kirakage88/thesis/schematics/kicad_templates-master/Alchitry_Au/meta/info.html

# Alchitry Shield Board

This template creates the basic layout for designing an Alchitry (https://alchitry.com/) shield

This base project includes the PCB edge with 4x 50-pin headers and mounting holes in the correct position. This also includes the footprint library and schmatic symbols for the bottom, male connectors. The connectors are numbered such that pin B1 aligns with pin X1 on the Alchitry board for easy reference to the Alchitry datasheet.

The board outline looks like the following:

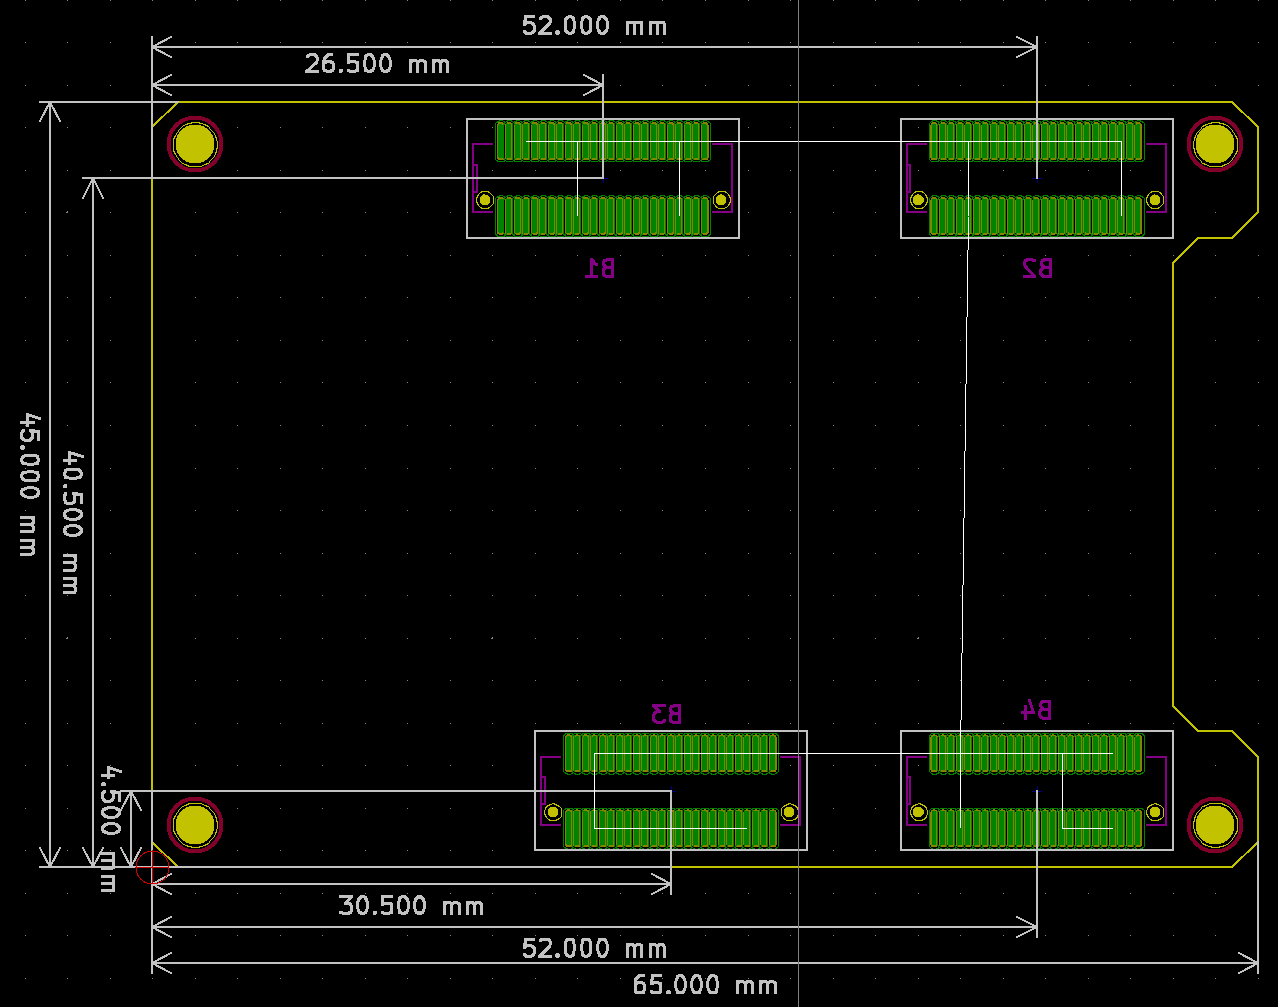
[picture p1: schematics/kicad_templates-master/Alchitry_Au/meta/board.png]
