kirakage88/thesis/designs/tft_display/assets/home_page.png

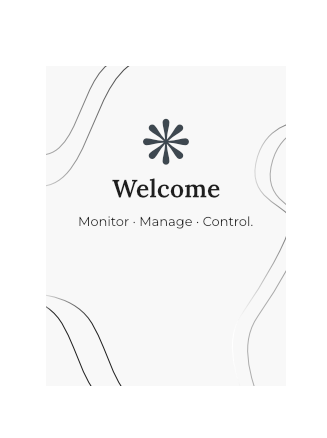
designs/tft_display/assets/home_page.png
