kirakage88/thesis/designs/tft_display/home_page.png

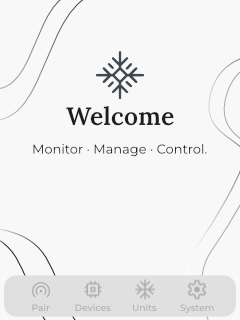
designs/tft_display/home_page.png
