kirakage88/thesis/designs/tft_display/init_page.png

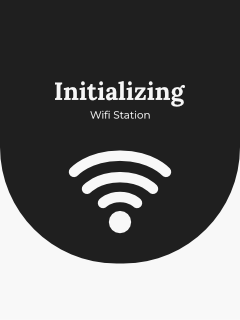
designs/tft_display/init_page.png
