kirakage88/thesis/designs/tft_display/palette_shades.png

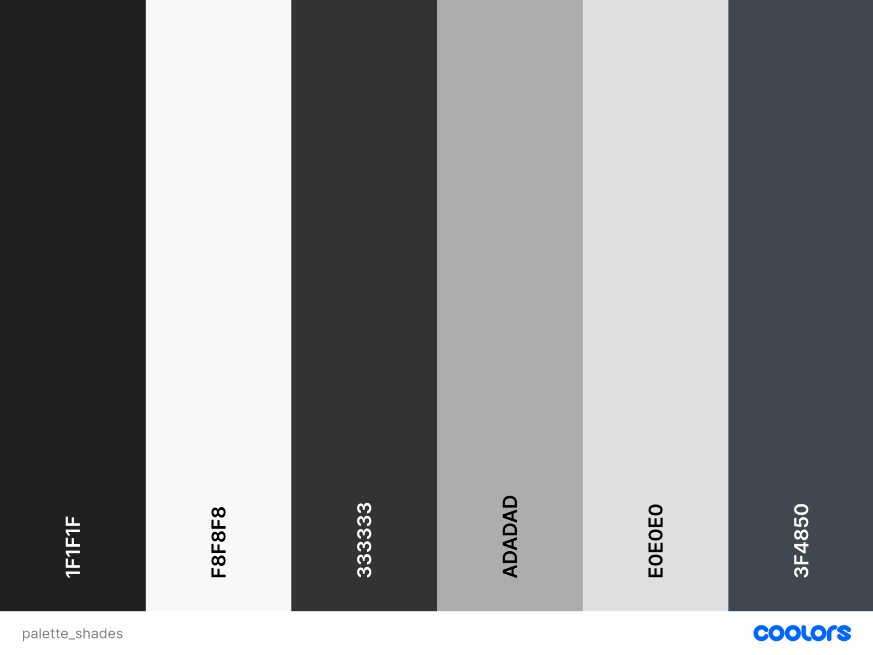
designs/tft_display/palette_shades.png
