kirakage88/thesis/designs/website/reference_website.jpg

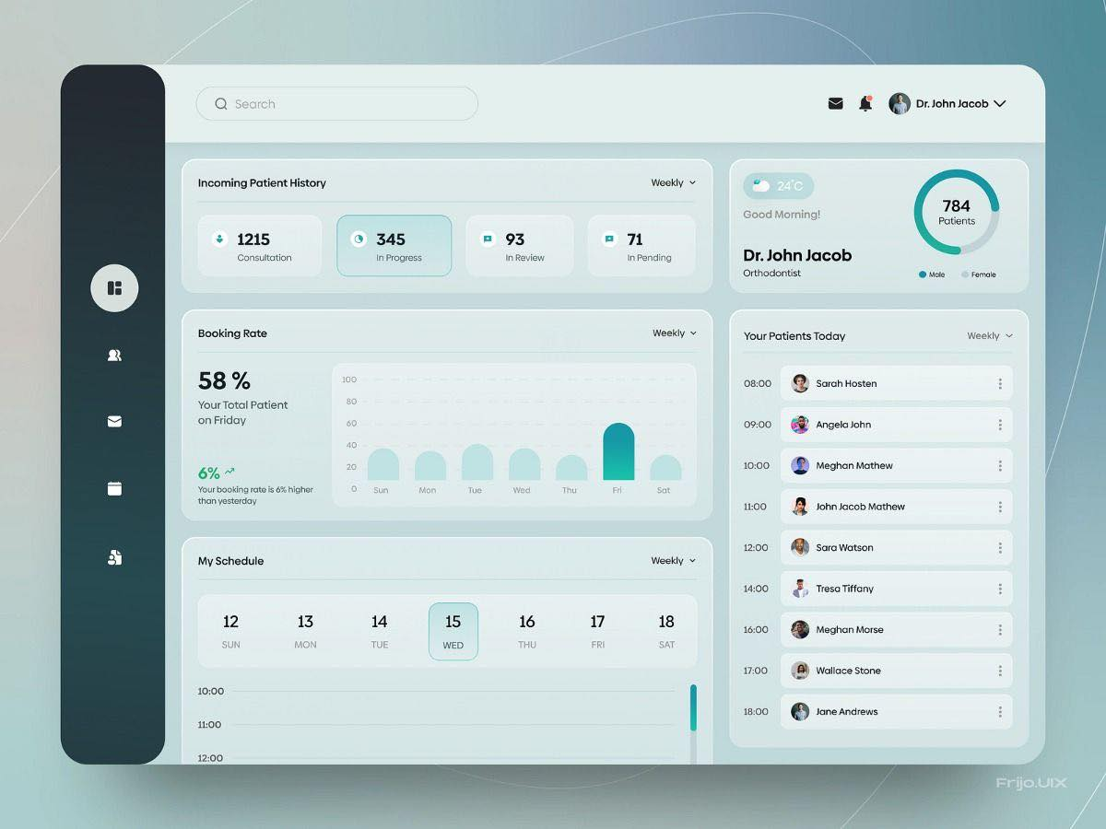
designs/website/reference_website.jpg
