kirakage88/thesis/schematics/BME 280 SOLO.jpg

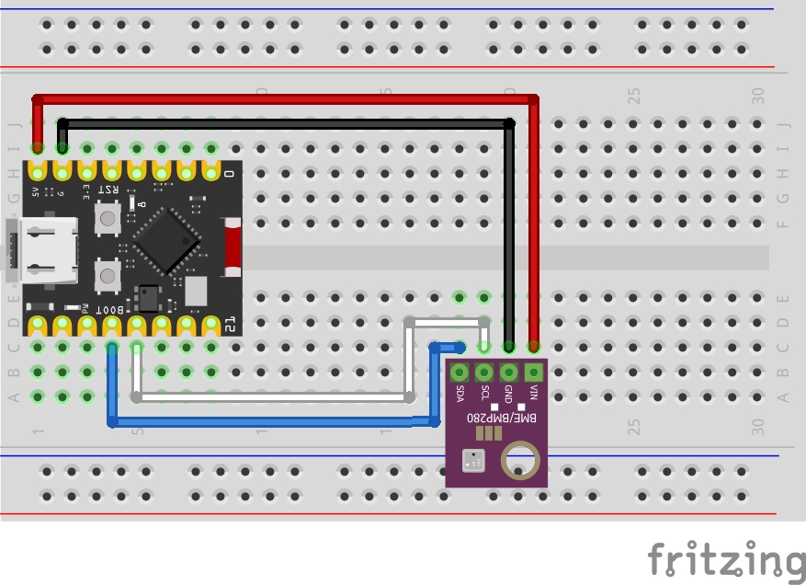
schematics/BME 280 SOLO.jpg
