kirakage88/thesis/schematics/RMS Prototype Ver 1_bb.png

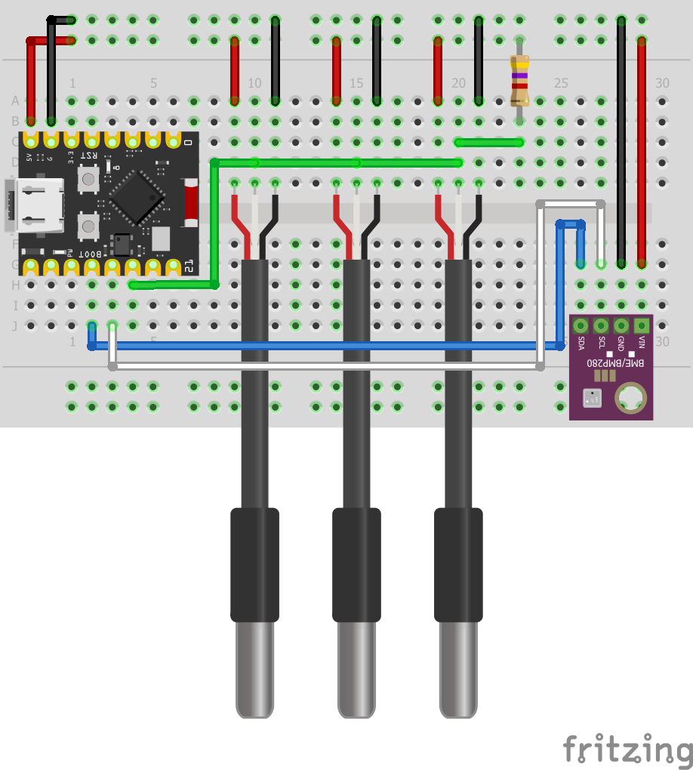
schematics/RMS Prototype Ver 1_bb.png
