kirakage88/thesis/schematics/TFT Display_schem.png

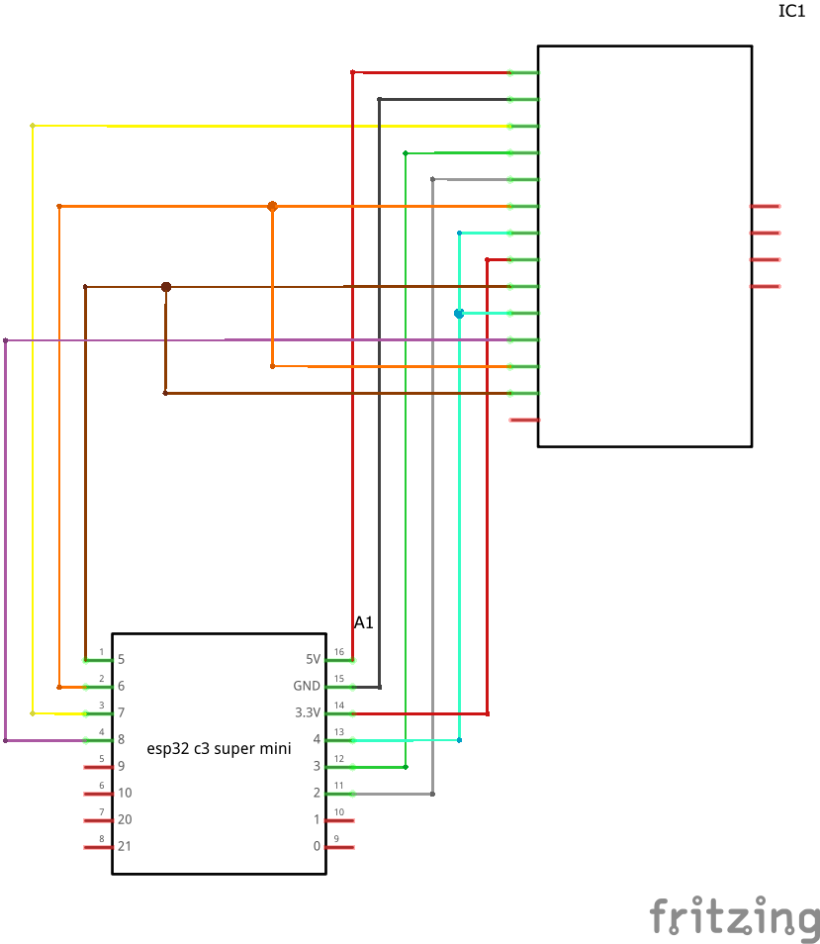
schematics/TFT Display_schem.png
