kirakage88/thesis/codes/python/machine learning/0 perceptron.py

from sklearn import datasets
from sklearn.model_selection import train_test_split
from sklearn.preprocessing import StandardScaler
from sklearn.linear_model import Perceptron
from sklearn.metrics import accuracy_score
from helper import plot_decision_regions
import matplotlib.pyplot as plt
import numpy as np

iris = datasets.load_iris()
X = iris.data[:, [2, 3]]
y = iris.target


X_train, X_test, y_train, y_test = train_test_split(X, y, test_size=0.3, random_state=1, stratify=y)

#print(f'Labels count in y: {np.bincount(y)}')
#print(f'Labels count in y_train: {np.bincount(y_train)}')
#print(f'Labels count in y_test: {np.bincount(y_test)}')

sc = StandardScaler()
sc.fit(X_train)
X_train_std = sc.transform(X_train)
X_test_std = sc.transform(X_test)

ppn = Perceptron(eta0=0.1, random_state=1)
ppn.fit(X_train_std, y_train)

y_pred = ppn.predict(X_test_std)
print('Misclassified examples: %d' % (y_test != y_pred).sum())
print('Accuracy: %.3f' % accuracy_score(y_test, y_pred))

X_combined_std = np.vstack((X_train_std, X_test_std))
y_combined = np.hstack((y_train, y_test))

plot_decision_regions(X=X_combined_std, y=y_combined, classifier=ppn, test_idx=range(105, 150))
plt.xlabel('Petal length [standardized]')
plt.ylabel('Petal width [standardized]')
plt.legend(loc='upper left')
plt.tight_layout()
plt.show()
